ohasanov-hbrw/tribit32-advanced/3D Files/TPS Holder Lid.step

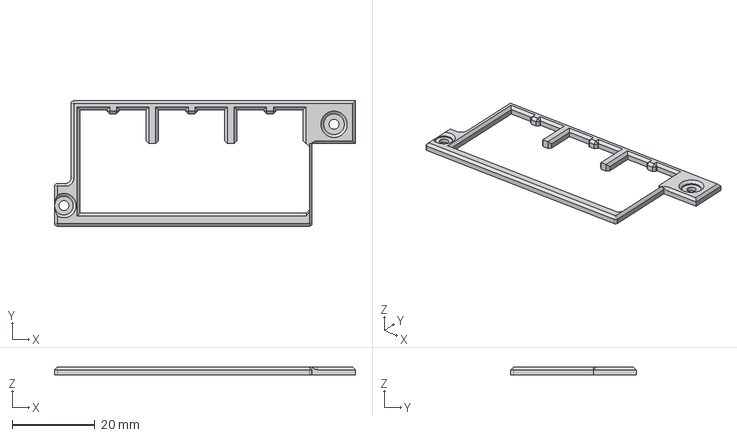
[picture p19: CAD file, 2026-08-13]
3D Files/TPS Holder Lid.step
72.9 x 30.4 x 2.00 mm
