ohasanov-hbrw/tribit32-advanced/3D Files/Switch Holder.step

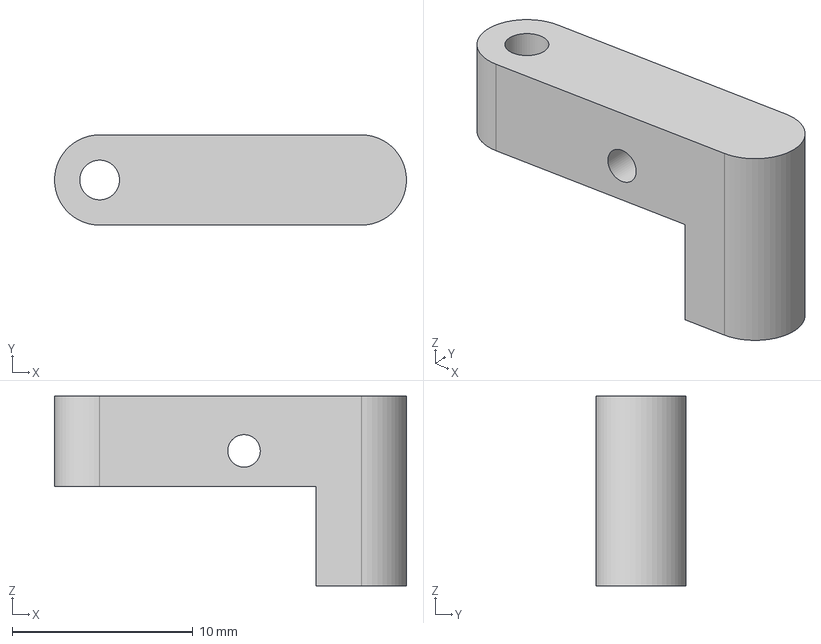
[picture p20: CAD file, 2026-08-13]
3D Files/Switch Holder.step
19.5 x 5.00 x 10.5 mm
