ohasanov-hbrw/tribit32-advanced/3D Files/Face Button Structure.step

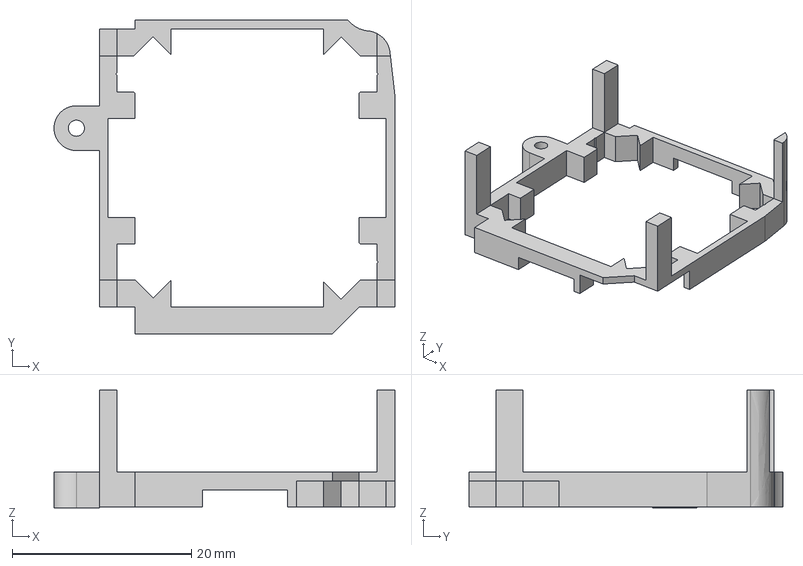
[picture p21: CAD file, 2026-08-13]
3D Files/Face Button Structure.step
38.1 x 35.0 x 13.1 mm
