ohasanov-hbrw/tribit32-advanced/3D Files/TP4056 Holder.step

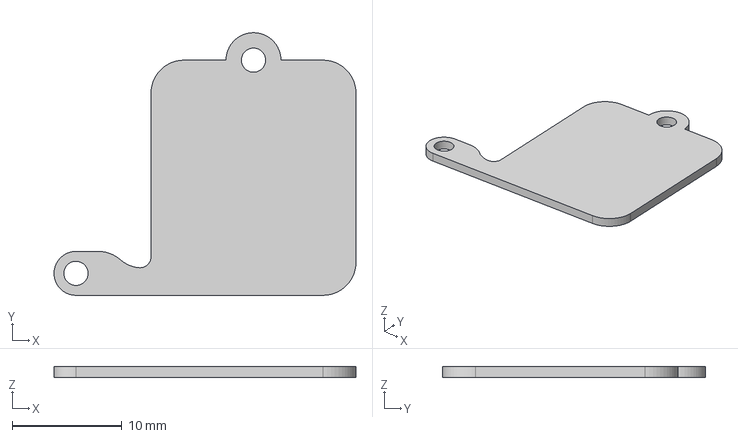
[picture p22: CAD file, 2026-08-13]
3D Files/TP4056 Holder.step
27.5 x 23.9 x 1.00 mm
