ohasanov-hbrw/tribit32-advanced/3D Files/Speaker Lid (also mirrored).step

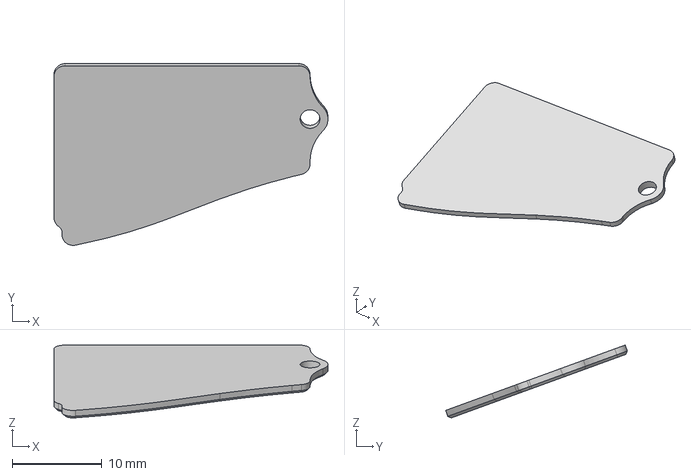
[picture p23: CAD file, 2026-08-13]
3D Files/Speaker Lid (also mirrored).step
30.5 x 20.2 x 8.11 mm
