ohasanov-hbrw/tribit32-advanced/Raspberry/boot_firmware/config.txt

# For more options and information see
# http://rptl.io/configtxt
# Some settings may impact device functionality. See link above for details

# Uncomment some or all of these to enable the optional hardware interfaces
#dtparam=i2c_arm=on
#dtparam=i2s=on
#dtparam=spi=on

# Enable audio (loads snd_bcm2835)
#dtparam=audio=on

# Additional overlays and parameters are documented
# /boot/firmware/overlays/README

# Automatically load overlays for detected cameras
#camera_auto_detect=1

# Automatically load overlays for detected DSI displays
#display_auto_detect=1

# Automatically load initramfs files, if found
auto_initramfs=1

# Enable DRM VC4 V3D driver
dtoverlay=vc4-fkms-v3d,audio=off
#max_framebuffers=3
gpu_mem=128
max_framebuffers=1
# Don't have the firmware create an initial video= setting in cmdline.txt.
# Use the kernel's default instead.
#disable_fw_kms_setup=1


# uncomment to force a console size. By default it will be display's size minus
# overscan.
#framebuffer_width=320
#framebuffer_height=240

# uncomment if hdmi display is not detected and composite is being output
#hdmi_force_hotplug=1
hdmi_ignore_edid=0xa5000080

# uncomment to force a specific HDMI mode (this will force VGA)
#hdmi_group=2
#hdmi_mode=4
#hdmi_cvt=320 240 60 1 0 0 0

#framebuffer_width=320
#framebuffer_height=240
#hdmi_group=2
#hdmi_mode=1
#hdmi_mode=87
#hdmi_cvt 320 240 60 6 0 0 0

#hdmi_force_hotplug=1
#hdmi_group=2
#hdmi_mode=4

hdmi_force_hotplug=1
hdmi_group=2
hdmi_mode=87
hdmi_cvt=640 480 60 1 0 0 0
framebuffer_width=640
framebuffer_height=480
max_framebuffer_width=640
max_framebuffer_height=480
#dtoverlay=pi3-miniuart-bt
# Disable compensation for displays with overscan
disable_overscan=1
dtoverlay=disable-bt
# Run as fast as firmware / board allows
#arm_boost=1

[cm4]
# Enable host mode on the 2711 built-in XHCI USB controller.
# This line should be removed if the legacy DWC2 controller is required
# (e.g. for USB device mode) or if USB support is not required.
otg_mode=1

[cm5]
dtoverlay=dwc2,dr_mode=host

[all]
#dtoverlay=disable-bt
enable_uart=1

dtoverlay=hifiberry-dac
#dtoverlay=max98357a
dtoverlay=i2s-mmap

#dtoverlay=googlevoicehat-soundcard
